mpt-d/printable-optical-mounts/cage/30mm/cage_mount-spiral.FCStd

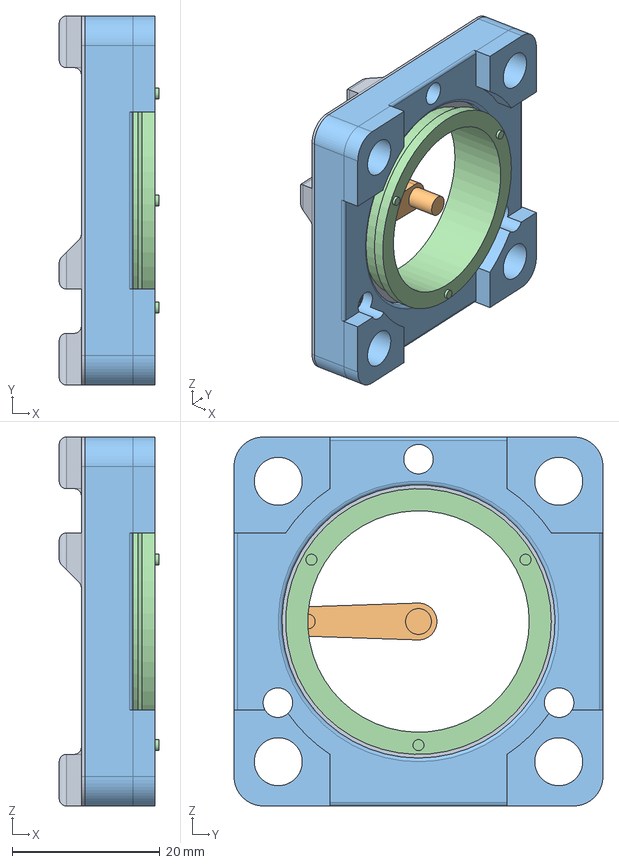
[picture p15: CAD file, 2023-03-16]
cage/30mm/cage_mount-spiral.FCStd
13.5 x 50.0 x 50.0 mm
front
back
bezel
