mpt-d/printable-optical-mounts/mounts/mount-tran_xy.FCStd

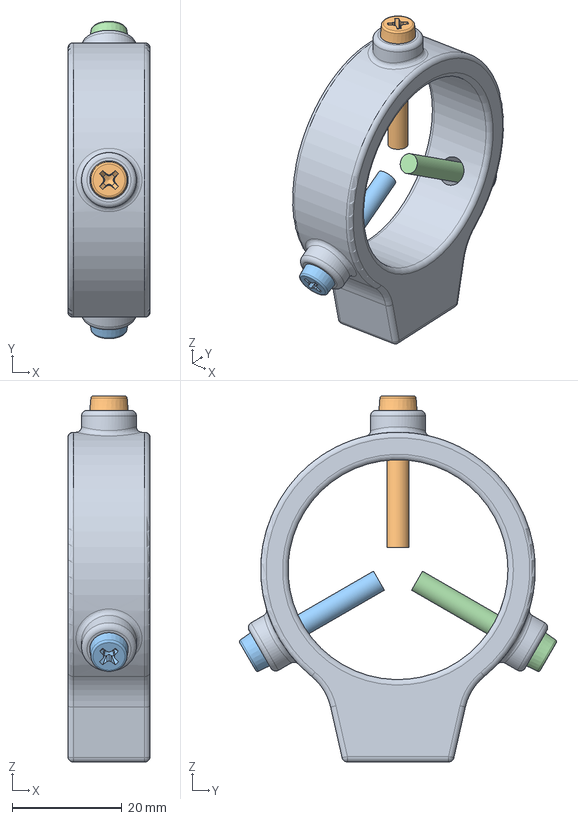
[picture p16: CAD file, 2023-03-16]
mounts/mount-tran_xy.FCStd
15.0 x 57.7 x 66.6 mm
mount-tran-xy
M4x25-Screw002
M4x25-Screw001
M4x25-Screw
