mpt-d/printable-optical-mounts/posts/pedestals.FCStd

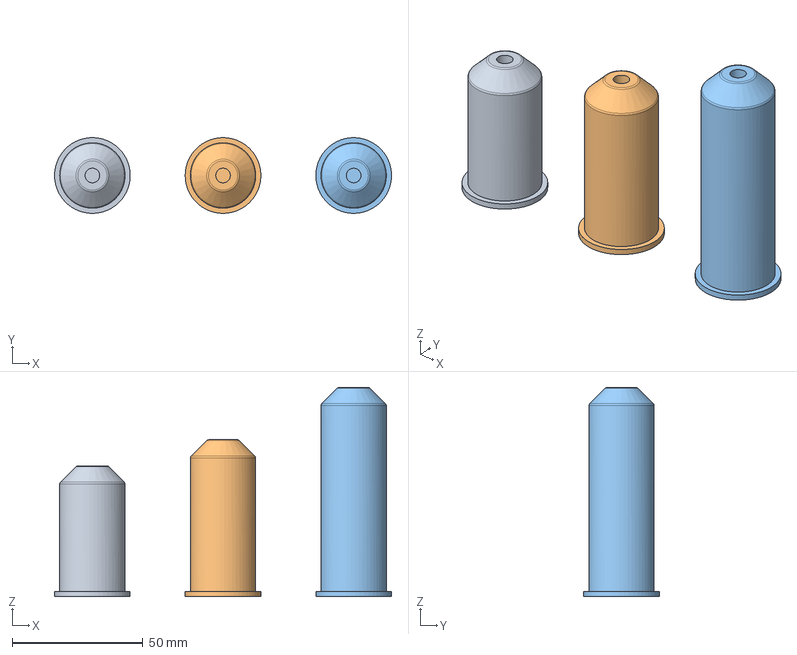
[picture p17: CAD file, 2023-03-16]
posts/pedestals.FCStd
129.0 x 29.0 x 80.0 mm
pedestal
pedestal001
pedestal002
