mpt-d/printable-optical-mounts/cage/30mm/cage_mount-tran_xy.FCStd

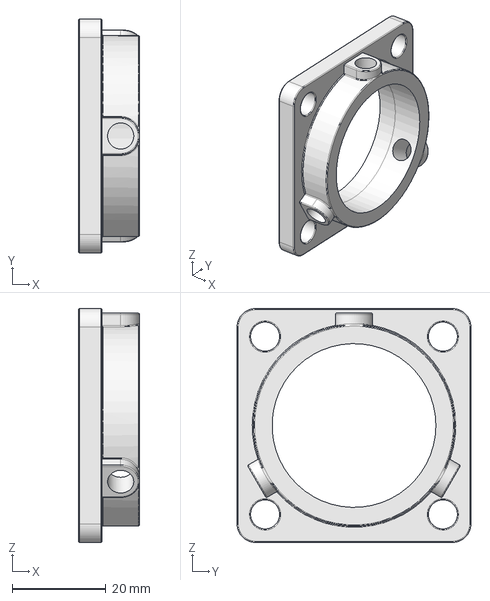
[picture p18: CAD file, 2023-03-16]
cage/30mm/cage_mount-tran_xy.FCStd
13.0 x 50.0 x 50.0 mm
