mpt-d/printable-optical-mounts/mounts/iris.FCStd

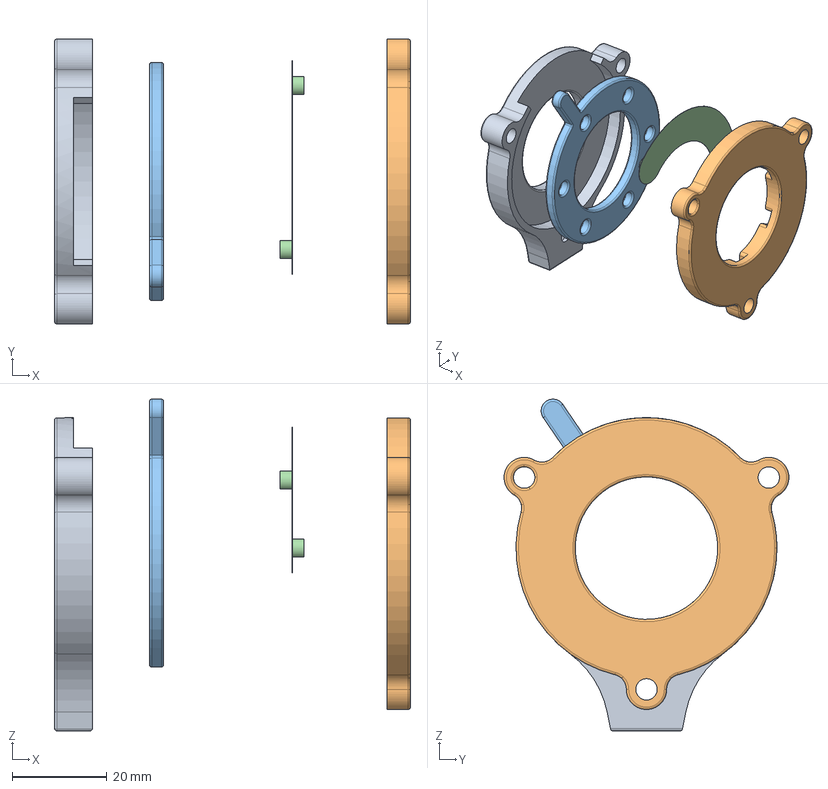
[picture p19: CAD file, 2023-03-16]
mounts/iris.FCStd
75.0 x 60.0 x 69.9 mm
back
front
ring
blade
