mpt-d/printable-optical-mounts/posts/post_holder.FCStd

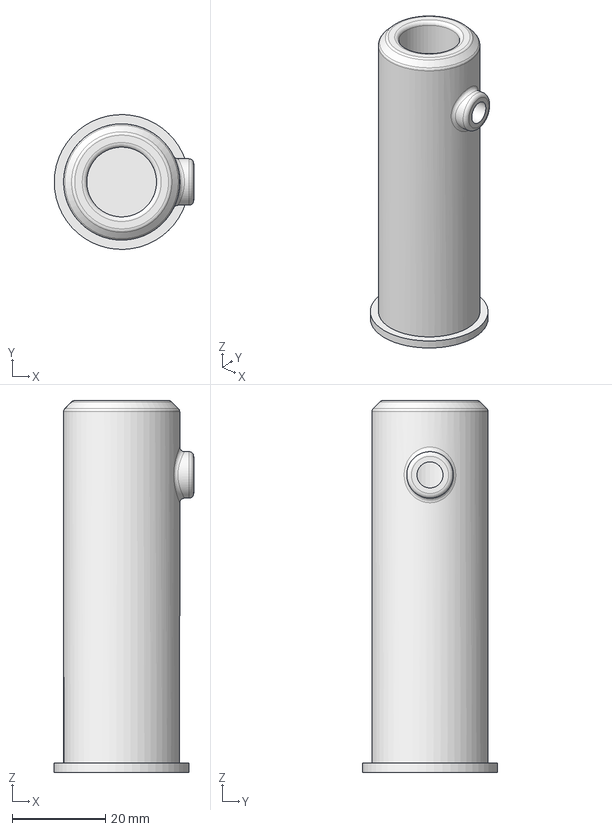
[picture p20: CAD file, 2023-03-16]
posts/post_holder.FCStd
30.0 x 29.0 x 80.0 mm
