mpt-d/printable-optical-mounts/cage/30mm/cage_mount-rot_xy.FCStd

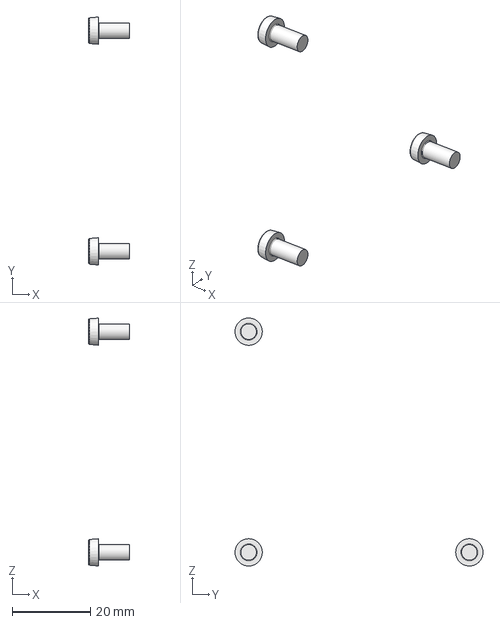
[picture p21: CAD file, 2023-03-16]
cage/30mm/cage_mount-rot_xy.FCStd
10.6 x 63.6 x 63.6 mm
M4x8-Screw x 3
