mpt-d/printable-optical-mounts/mounts/mount-rot_xy.FCStd

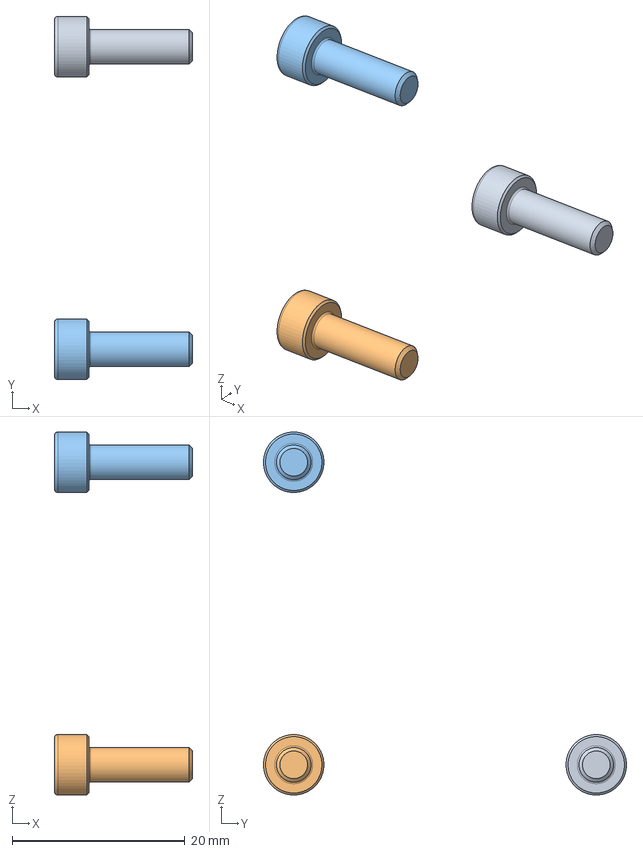
[picture p22: CAD file, 2023-03-16]
mounts/mount-rot_xy.FCStd
16.0 x 42.0 x 42.0 mm
M4x12-Screw
M4x12-Screw005
M4x12-Screw006
