mpt-d/printable-optical-mounts/cage/30mm/junction-side.FCStd

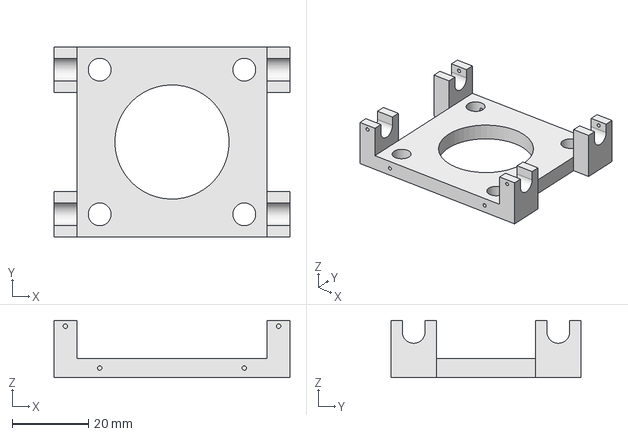
[picture p23: CAD file, 2023-03-16]
cage/30mm/junction-side.FCStd
62.0 x 50.0 x 15.0 mm
