mpt-d/printable-optical-mounts/cage/30mm/post_mount.FCStd

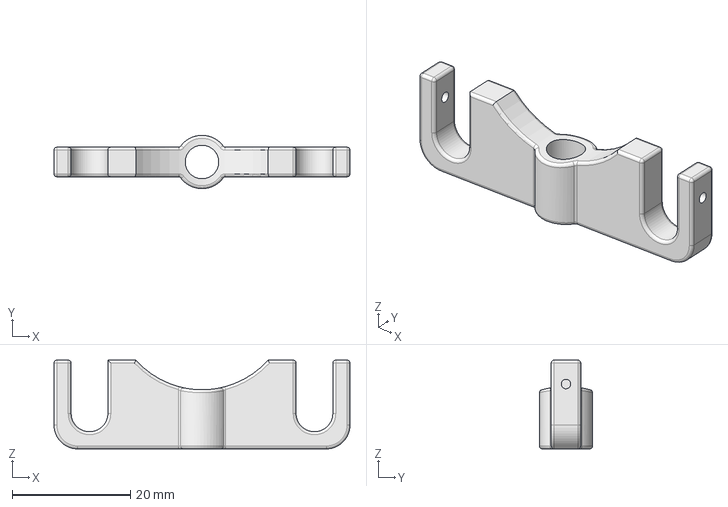
[picture p24: CAD file, 2023-03-16]
cage/30mm/post_mount.FCStd
50.0 x 9.00 x 15.0 mm
