mpt-d/printable-optical-mounts/cage/30mm/pole_to_pole_tie.FCStd

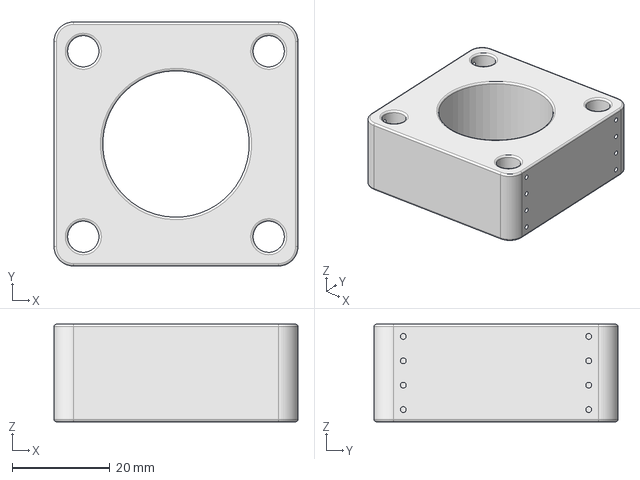
[picture p25: CAD file, 2023-03-16]
cage/30mm/pole_to_pole_tie.FCStd
50.0 x 50.0 x 20.0 mm
