mpt-d/printable-optical-mounts/cage/30mm/cage_mount-filter_mirror.FCStd

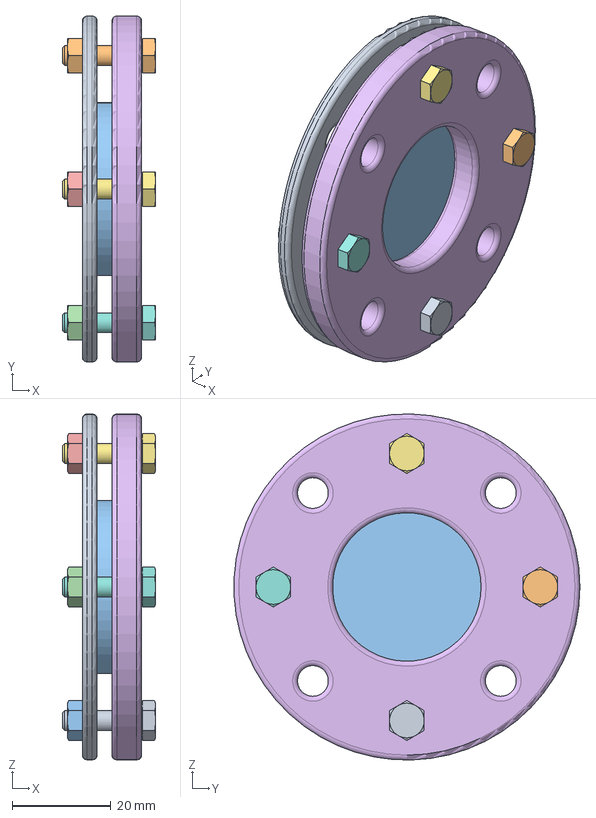
[picture p26: CAD file, 2023-03-16]
cage/30mm/cage_mount-filter_mirror.FCStd
18.8 x 69.9 x 70.0 mm
front
M4-Nut
M4-Nut001
M4-Nut002
M4-Nut003
back
M4x16-Screw
M4x16-Screw001
M4x16-Screw002
M4x16-Screw003
Filter
