mpt-d/printable-optical-mounts/cage/30mm/pole.FCStd

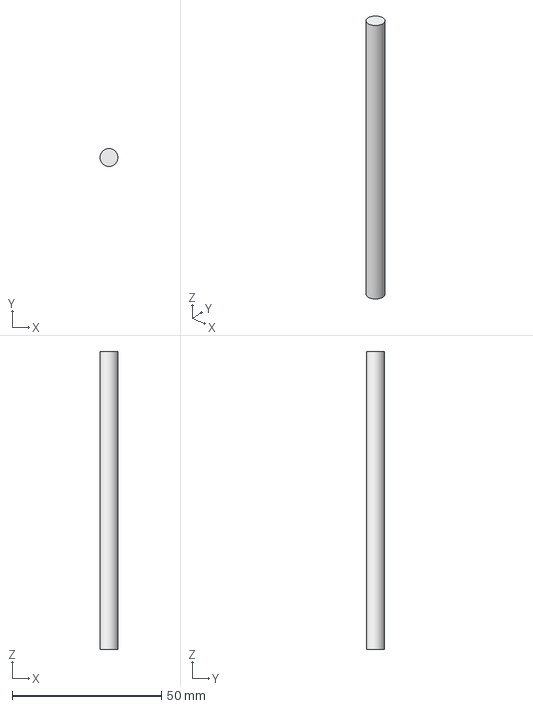
[picture p27: CAD file, 2023-02-24]
cage/30mm/pole.FCStd
5.99 x 6.00 x 100.0 mm
